willem-pennings/table-tennis-scoreboard/software/scoreboard-controller/src/scoreboard-controller.h

// Include definitions.
#include "definitions/parameters.h"
#include "definitions/pins.h"
#include "definitions/secrets.h"

// Include classes.
#include "classes/counter_base.h"
#include "classes/game_counter.h"
#include "classes/score_counter.h"
#include "classes/scoreboard_server.h"
#include "classes/segment.h"
#include "classes/timeout_indicator.h"
#include "classes/umpire.h"
